al83012/Informatik-Q12---Micromouse/3DP/LED_Holder.3mf

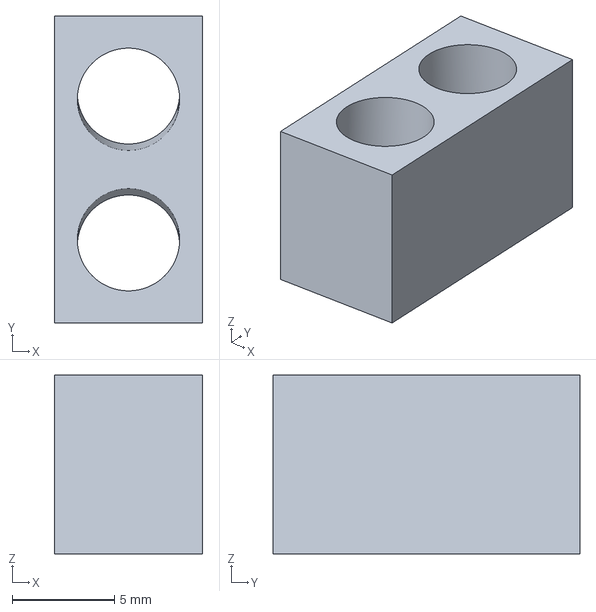
[picture p3: CAD file, 2026-06-30]
3DP/LED_Holder.3mf
7.25 x 15.0 x 8.75 mm
