al83012/Informatik-Q12---Micromouse/micromouse_control/include/driveControl.h

#ifndef drivecontrol_h
#define drivecontrol_h

namespace DRIVECONTROL {
    void forward(float distanceCm, float baseSpeedPercentage);
    void backward(float distanceCm, float baseSpeedPercentage);
    void setPIDParameters(float Kp, float Ki, float Kd);
    void resetEncoders();

    void simpleForward1(float distanceCm, float baseSpeedPercentage);
}

#endif
