al83012/Informatik-Q12---Micromouse/micromouse_control/src/Components/tmp464.cpp

#include "Components/TMP464.h"
#include "Arduino.h"
#include "Components/esp32.h"
#include "i2ctool.h"
#include "colors.h"

using namespace COLORS;
// Temperature Sensor
using namespace TMP464;
using namespace I2CTOOL;
using namespace Measurement::Sensors;


void TMP464::init() {
    // Initialize the TMP464 temperature sensor
    findComponent(Measurement::Sensors::SensorNames::TMP464_TEMPERATURE_SENSOR);
    uint16_t remoteOpenChannels;
    I2C1Read(ComponentVars::I2C_ADDRESS, 0x23, remoteOpenChannels);
    log_d("Open remote channels, %d", remoteOpenChannels);

    setStandardConfiguration();

}
void TMP464::setStandardConfiguration() {
     log_d("# (TMP464) Trying to set standard configuration");
    I2C1Write(ComponentVars::I2C_ADDRESS, ComponentVars::REG_CONFIG, ComponentVars::SETTINGS_REG_CONFIG);
}

float TMP464::readLocalTemperature() {
    log_d("# (TMP464) Trying to read local temperature");
    uint16_t rawTemp;
     I2C1Read(ComponentVars::I2C_ADDRESS, ComponentVars::REG_LOCAL_TEMP, rawTemp);
    return convertToCelsius(rawTemp);
}

float TMP464::readRemoteTemperature(uint8_t channel) {
    log_d("# (TMP464) Trying to read remote temperature on channel %d", channel);
    //Channel 1 = 0x01 ; Channel 2 = 0x02 ; Channel 3 = 0x03 ; Channel 4 = 0x04
    uint16_t rawTemp;
    I2C1Read(ComponentVars::I2C_ADDRESS, ComponentVars::REG_REMOTE_TEMP + (channel - 1), rawTemp); 
    return convertToCelsius(rawTemp);
}

float TMP464::convertToCelsius(uint16_t rawValue) {
    //log_d("# (TMP464) Converting temperature... %d", rawValue );
    int16_t signedTemp = (int16_t)rawValue; 
    //log_d("# Raw HEX (Shifted): %X", (signedTemp >> 3));
    signedTemp >>=3;
    return (static_cast<float>(signedTemp) * 0.0625f); //Shift 3 bits, since data is only stored in the upper 13 bits (resolution of 0.0625 - fixed)
}

void TMP464::setLocalThermLimit(uint16_t limit) {
    if(limit > 256) {
    log_e(RED "# Invalid temperature limit (LocalTempLimit - TMP464)!");
    uint16_t formatted_limit = limit << 8;
    } else {
    I2C1Write(ComponentVars::I2C_ADDRESS, ComponentVars::REG_LOCAL_THERM_LIMIT, limit);
    }
}

void TMP464::setLocalTherm2Limit(uint16_t limit) {
    if(limit > 256) {
    log_e(RED "# Invalid temperature limit2 (LocalTempLimit2 - TMP464)!");
    uint16_t formatted_limit = limit << 8;
    } else {
    I2C1Write(ComponentVars::I2C_ADDRESS, ComponentVars::REG_LOCAL_THERM2_LIMIT, limit);
    }
}

void TMP464::setRemoteThermLimit(uint8_t channel, uint16_t limit) {
    log_d("# (TMP464) Trying to set RemoteTemp Limit %d", limit , "for channel %d", channel);
    if(limit > 256) {
    log_e(RED "# Invalid temperature limit (RemoteTemp - TMP464)!");
    uint16_t formatted_limit = limit << 8;
    } else {
    
    if(channel == 1) {
        I2C1Write(ComponentVars::I2C_ADDRESS, ComponentVars::REG_REMOTE_1_THERM_LIMIT, limit);
    } else if(channel == 2) {
        I2C1Write(ComponentVars::I2C_ADDRESS, ComponentVars::REG_REMOTE_2_THERM_LIMIT, limit);
    } else if(channel == 3) {
        I2C1Write(ComponentVars::I2C_ADDRESS, ComponentVars::REG_REMOTE_3_THERM_LIMIT, limit);
    } else if(channel == 4) {
        I2C1Write(ComponentVars::I2C_ADDRESS, ComponentVars::REG_REMOTE_4_THERM_LIMIT, limit);
    } else {
        log_e(RED "# (TMP464) Error while trying to set remote temperature: Invalid channel!");
    }

    }

}

void TMP464::setRemoteTherm2Limit(uint8_t channel, uint16_t limit) {
    log_d("# (TMP464) Trying to set RemoteTemp Limit %d", limit , "for channel %d", channel);
    if(limit > 256) {
    log_e(RED "# Invalid temperature limit (RemoteTemp - TMP464)!");
    uint16_t formatted_limit = limit << 8;
    } else {
    
    if(channel == 1) {
        I2C1Write(ComponentVars::I2C_ADDRESS, ComponentVars::REG_REMOTE_1_THERM2_LIMIT, limit);
    } else if(channel == 2) {
        I2C1Write(ComponentVars::I2C_ADDRESS, ComponentVars::REG_REMOTE_2_THERM2_LIMIT, limit);
    } else if(channel == 3) {
        I2C1Write(ComponentVars::I2C_ADDRESS, ComponentVars::REG_REMOTE_3_THERM2_LIMIT, limit);
    } else if(channel == 4) {
        I2C1Write(ComponentVars::I2C_ADDRESS, ComponentVars::REG_REMOTE_4_THERM2_LIMIT, limit);
    } else {
        log_e(RED "# (TMP464) Error while trying to set remote temperature: Invalid channel!");
    }

    }
}

void TMP464::setGlobalThermLimits(uint16_t lowestSafeTemp, uint16_t highestSafeTemp) {

    log_d("# (TMP464) Trying to set global temperature limits");

    setLocalThermLimit(lowestSafeTemp);
    setLocalTherm2Limit(highestSafeTemp);

    setRemoteThermLimit(1, lowestSafeTemp);
    setRemoteTherm2Limit(1, highestSafeTemp);

    setRemoteThermLimit(2, lowestSafeTemp);
    setRemoteTherm2Limit(2, highestSafeTemp);

    setRemoteThermLimit(3, lowestSafeTemp);
    setRemoteTherm2Limit(3, highestSafeTemp);

    setRemoteThermLimit(4, lowestSafeTemp);
    setRemoteTherm2Limit(4, highestSafeTemp);

}

void TMP464::setShutdownMode(bool enableShutDown) {
    log_d("# Trying to enable shutdown mode (TMP464)");
    uint16_t current_reg;
    I2C1Read(ComponentVars::I2C_ADDRESS, ComponentVars::REG_CONFIG, current_reg);
    if(enableShutDown) {
        current_reg |= (1 << 5);
        log_d(GREEN "# Succesfuly enabled shutdown mode! (TMP464) " RESET);
    } else {
        log_d(GREEN "# Succesfuly disabled shutdown mode! (TMP464) " RESET);
        current_reg &= ~(1 << 5);
    }

    I2C1Write(ComponentVars::I2C_ADDRESS, ComponentVars::REG_CONFIG, current_reg);

}

void TMP464::DbgPrintTemperatures() {
    log_i("---------TEMPERATURES (TMP464)---------");
    log_i("# LOCAL: " GREEN "%f" RESET, readLocalTemperature() ) ;
    log_i("# REMOTE_1:" RED "%f" RESET, readRemoteTemperature(0x01) );
    log_i("# REMOTE_2: " RED "%f" RESET, readRemoteTemperature(0x02) );
    log_i("# REMOTE_3: " RED "%f" RESET, readRemoteTemperature(0x03) );
   // log_i("# REMOTE_4: " RED "%f" RESET, readRemoteTemperature(0x04)); Not connected
    log_i("---------------------------------------");


}
