al83012/Informatik-Q12---Micromouse/micromouse_control/include/colors.h

#ifndef colors_h
#define colors_h

namespace COLORS {
    #define RESET "\033[0m"
    #define RED     "\033[31m"
    #define GREEN   "\033[32m"
    #define YELLOW  "\033[33m"
    #define BLUE    "\033[34m"
    #define MAGENTA "\033[35m"
    #define CYAN    "\033[36m"
    #define WHITE   "\033[37m"

}

#endif
