al83012/Informatik-Q12---Micromouse/micromouse_control/include/utility.h

#ifndef UTILITY_H
#define UTILITY_H

#include <string>
#include <vector>
using namespace std;

namespace Utility {

    void printClient(string message);
    void stop();
    void restart();
    void debug(string message);
    void finishedAll();
    void finishedAllInterrupt(string message);
    void desync();    
    void sensor(string name, float value);
    std::vector<string> splitString(string str, char delimiter);
    


}

#endif
